YTenebris-STM/STM32_MeteoStation/Core/sys_data.h

#ifndef SYS_DATA_H
#define SYS_DATA_H

#include "stm32f10x.h"

// Configure weather data structure

typedef struct
{
	uint8_t     seconds;
	uint8_t     minutes;
	uint8_t     hours;
	const char* week;
	uint8_t     day;
	uint8_t     month;
	uint8_t     year;
} TimeData;

typedef struct 
{
	int32_t     temp;         // °C * 100
	uint32_t    press;        // Pa
	uint32_t    humid;        // % * 100
	uint16_t    uv;           // index (0...11)
	uint8_t     zmbr;         // index (1...26)
	uint16_t    wind_speed;   // mps * 100
	int16_t     apptemp;      // °C * 10
} MeteoData;

typedef struct
{
	TimeData* time;
	MeteoData* meteo;
} SystemData;

extern SystemData sys;

#endif
