YTenebris-STM/STM32_MeteoStation/Core/tasks.h

#ifndef TASKS_H
#define TASKS_H

void Task_Display (void);
void Task_BME280 (void);
void Task_UVI (void);
void Task_RTC (void);
void Task_Zambretti (void);
void Task_LED (void);
void Task_AppTemp (void);
void Task_Anemo (void);

#endif
